VedDevs/PocketVault/PCB/PocketVault/PocketVault.kicad_sch

## KiCad design PCB/PocketVault/PocketVault.kicad_sch (2026-06-18)

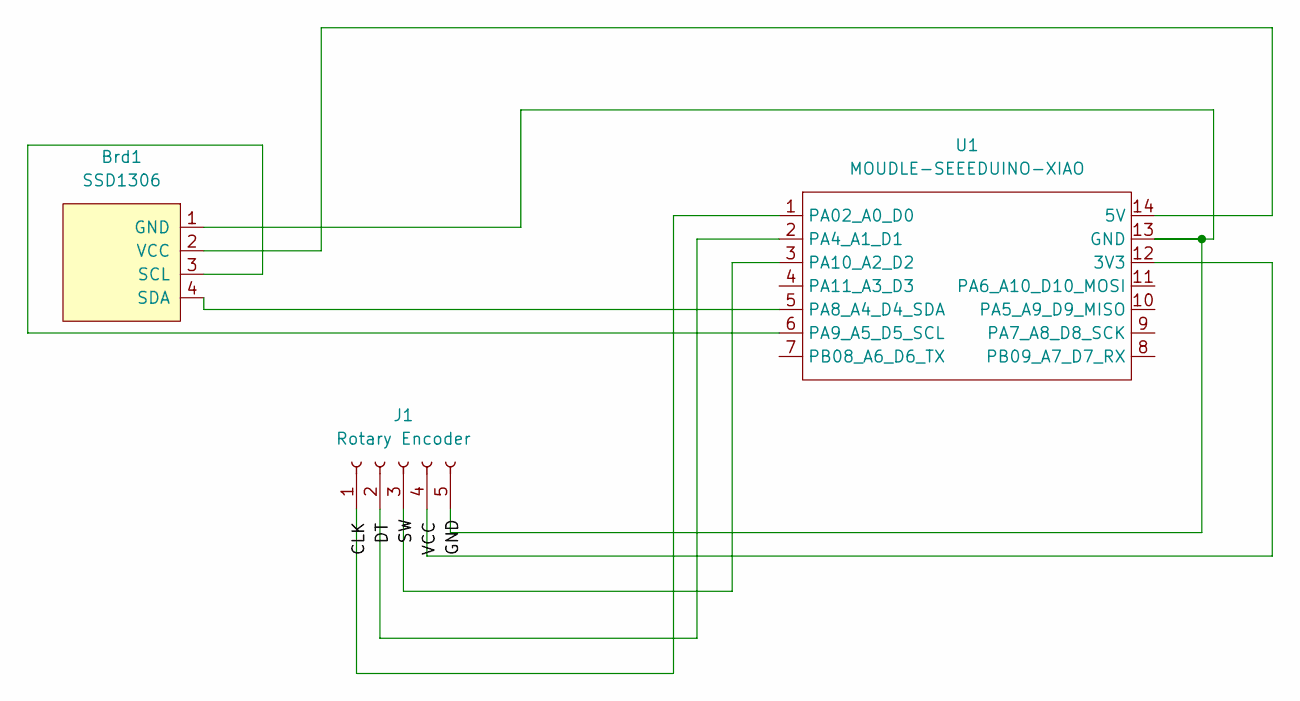
[picture p11: schematic PocketVault.kicad_sch]

Parts:
Brd1: SSD1306; 128x64OLED
J1: Rotary Encoder; PinHeader_1x05_P2.54mm_Vertical
U1: MOUDLE-SEEEDUINO-XIAO; XIAO-Generic-Hybrid-14P-2.54-21X17.8MM

Connections:
GND: J1.4, U1.12 (3V3)
unnamed: Brd1.1 (GND), J1.5, U1.13 (GND)
unnamed: Brd1.2 (VCC), U1.14 (5V)
unnamed: Brd1.3 (SCL), U1.6 (PA9_A5_D5_SCL)
unnamed: Brd1.4 (SDA), U1.5 (PA8_A4_D4_SDA)
unnamed: J1.1, U1.1 (PA02_A0_D0)
unnamed: J1.2, U1.2 (PA4_A1_D1)
unnamed: J1.3, U1.3 (PA10_A2_D2)
